aminnie/Ketron-EVM-MIDI-Controller/case/keycaps/roundedcubes.scad

//https://danielupshaw.com/openscad-rounded-corners/

// Higher definition curves
$fs = 0.01;

module roundedcube(size = [1, 1, 1], center = false, radius = 0.5, apply_to = "all") {
	// If single value, convert to [x, y, z] vector
	size = (size[0] == undef) ? [size, size, size] : size;

	translate_min = radius;
	translate_xmax = size[0] - radius;
	translate_ymax = size[1] - radius;
	translate_zmax = size[2] - radius;

	diameter = radius * 2;

	module build_point(type = "sphere", rotate = [0, 0, 0]) {
		if (type == "sphere") {
			sphere(r = radius);
		} else if (type == "cylinder") {
			rotate(a = rotate)
			cylinder(h = diameter, r = radius, center = true);
		}
	}

	obj_translate = (center == false) ?
		[0, 0, 0] : [
			-(size[0] / 2),
			-(size[1] / 2),
			-(size[2] / 2)
		];

	translate(v = obj_translate) {
		hull() {
			for (translate_x = [translate_min, translate_xmax]) {
				x_at = (translate_x == translate_min) ? "min" : "max";
				for (translate_y = [translate_min, translate_ymax]) {
					y_at = (translate_y == translate_min) ? "min" : "max";
					for (translate_z = [translate_min, translate_zmax]) {
						z_at = (translate_z == translate_min) ? "min" : "max";

						translate(v = [translate_x, translate_y, translate_z])
						if (
							(apply_to == "all") ||
							(apply_to == "xmin" && x_at == "min") || (apply_to == "xmax" && x_at == "max") ||
							(apply_to == "ymin" && y_at == "min") || (apply_to == "ymax" && y_at == "max") ||
							(apply_to == "zmin" && z_at == "min") || (apply_to == "zmax" && z_at == "max")
						) {
							build_point("sphere");
						} else {
							rotate = 
								(apply_to == "xmin" || apply_to == "xmax" || apply_to == "x") ? [0, 90, 0] : (
								(apply_to == "ymin" || apply_to == "ymax" || apply_to == "y") ? [90, 90, 0] :
								[0, 0, 0]
							);
							build_point("cylinder", rotate);
						}
					}
				}
			}
		}
	}
}

color("Yellow")
roundedcube(3, true, 0.7, "xmin");

//translate(v = [1, 0, 2])
//color("Pink")
//roundedcube([4, 2, 2], false, 0.6, "zmax");

//translate(v = [-4, -1, 2])
//color("Lightblue")
//roundedcube(2, false);

//translate(v = [0, 0, 6])
//color("Orange")
//roundedcube([3, 2, 2], true, 0.2);

//translate(v = [2.5, -0.5, 5])
//color("Green")
//roundedcube([3, 2, 2], false, 0.4, "z");
